bigbrainlabs/BoatOpenIO/images/v1_proto/1000084661.jpg

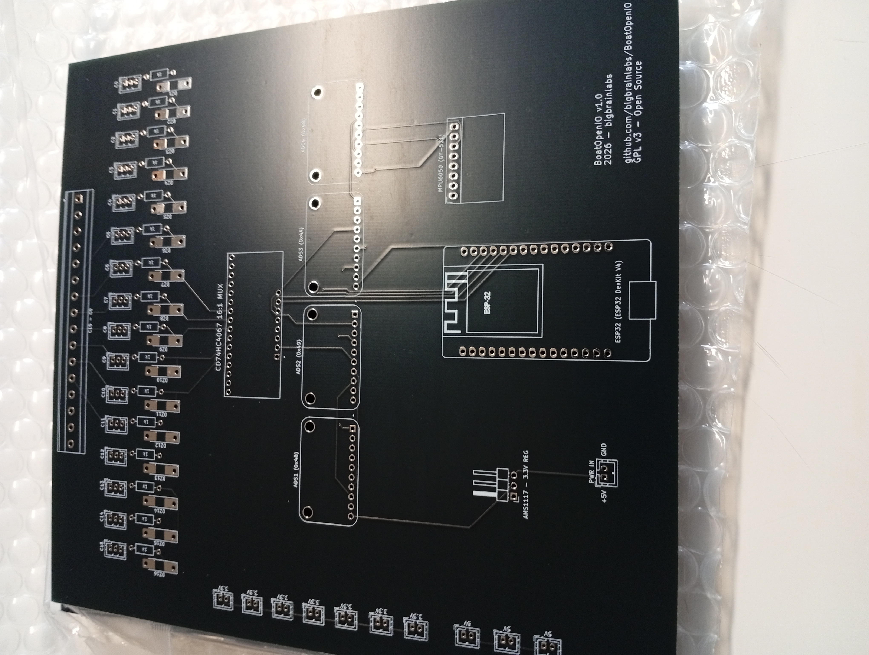
images/v1_proto/1000084661.jpg
