bigbrainlabs/BoatOpenIO/images/v1_proto/1000084662.jpg

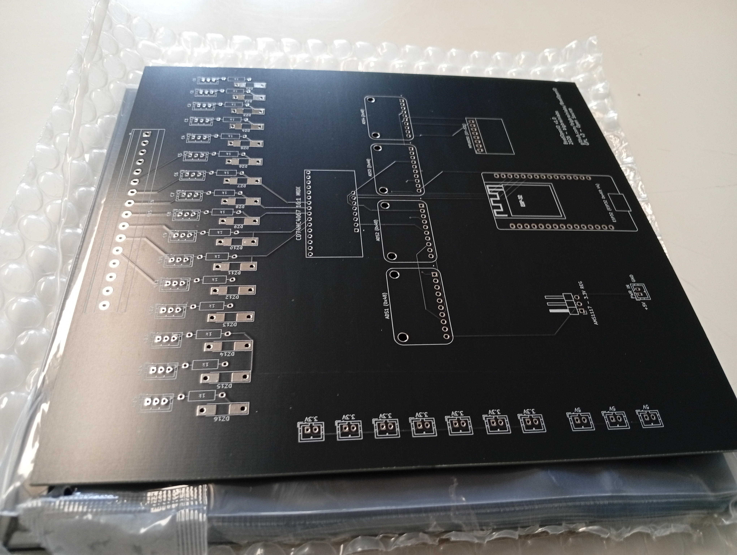
images/v1_proto/1000084662.jpg
