bigbrainlabs/BoatOpenIO/images/v1_proto/IMG_20260604_133746.jpg

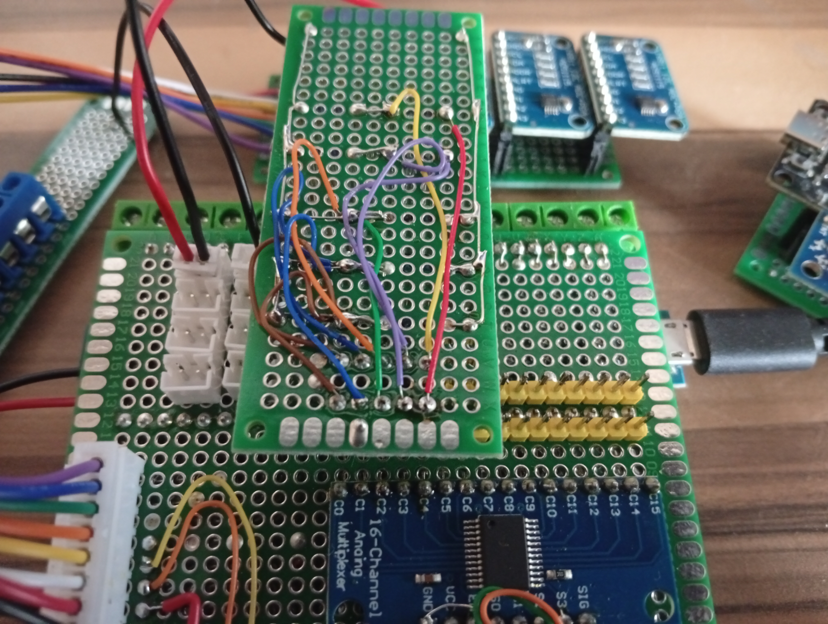
images/v1_proto/IMG_20260604_133746.jpg
